antonixus/JotPrintBot/assembly/assets/photos/photo_3.jpg

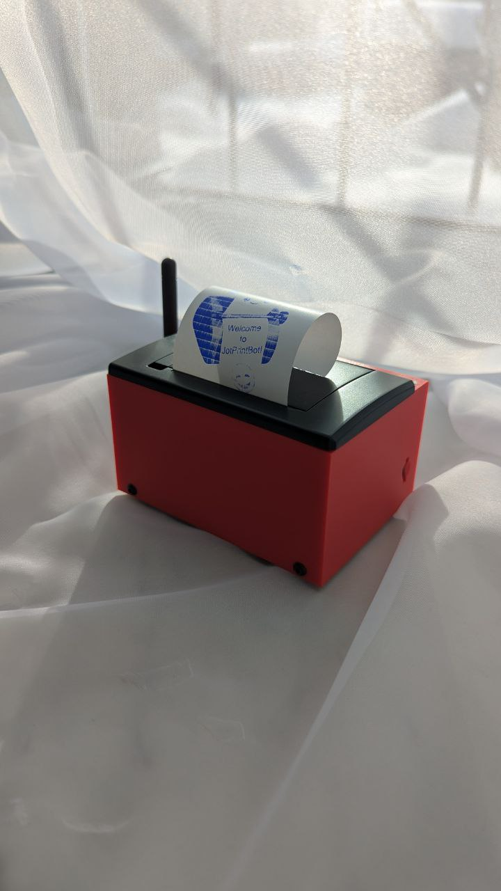
assembly/assets/photos/photo_3.jpg
