antonixus/JotPrintBot/assembly/assets/photos/photo_4.jpg

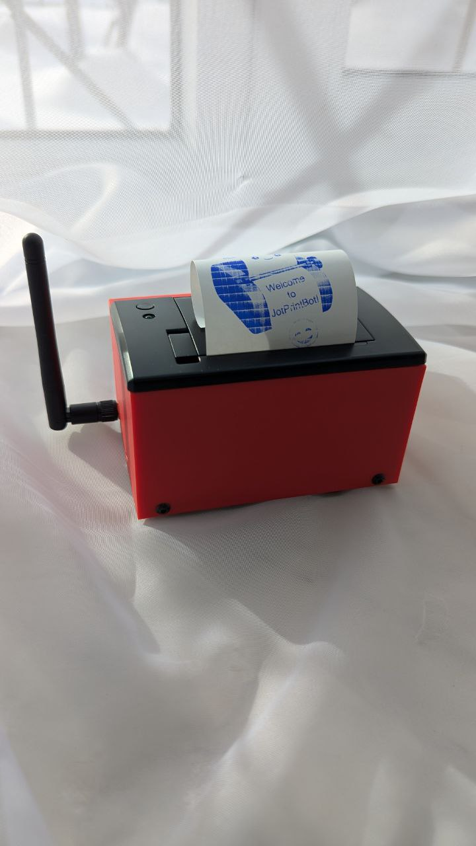
assembly/assets/photos/photo_4.jpg
