antonixus/JotPrintBot/assembly/assets/print_profile.png

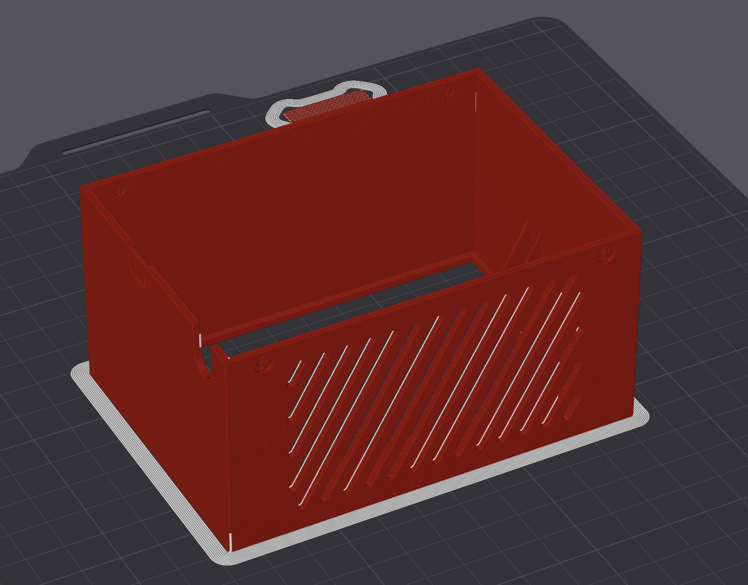
assembly/assets/print_profile.png
