antonixus/JotPrintBot/assembly/assets/render_4.png

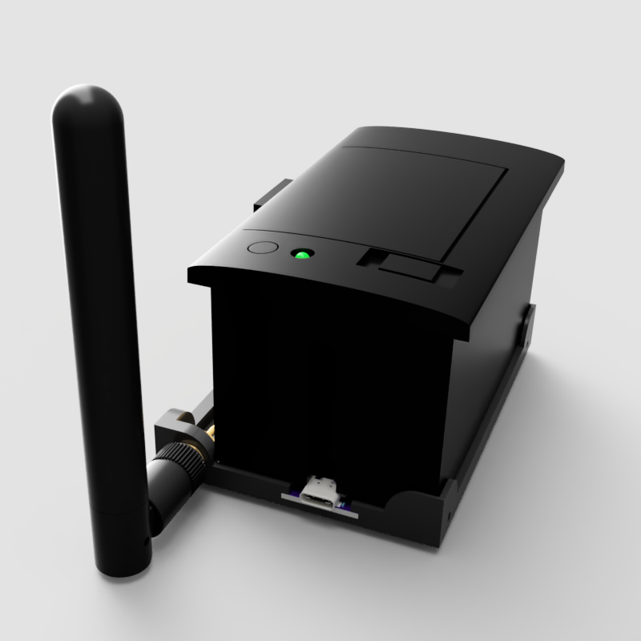
assembly/assets/render_4.png
